AnMe3z/VMKS/hardware/exports/exoskeleton parts-Short part.stl

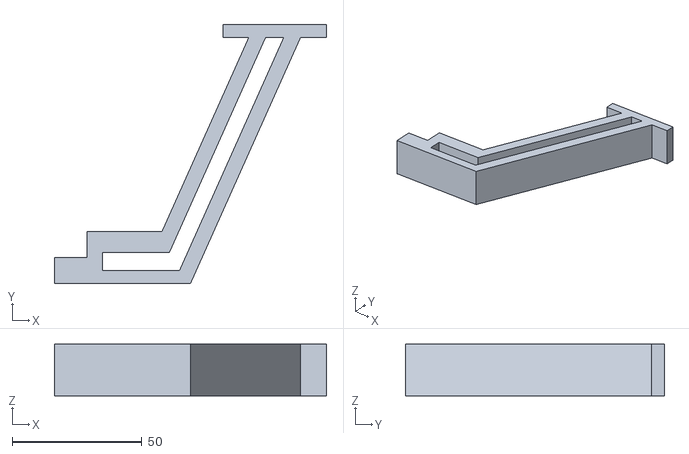
[picture p24: CAD file, 2023-04-21]
hardware/exports/exoskeleton parts-Short part.stl
105.0 x 100.0 x 20.0
