AnMe3z/VMKS/hardware/holders/ultrasonicHolder-Body.stl

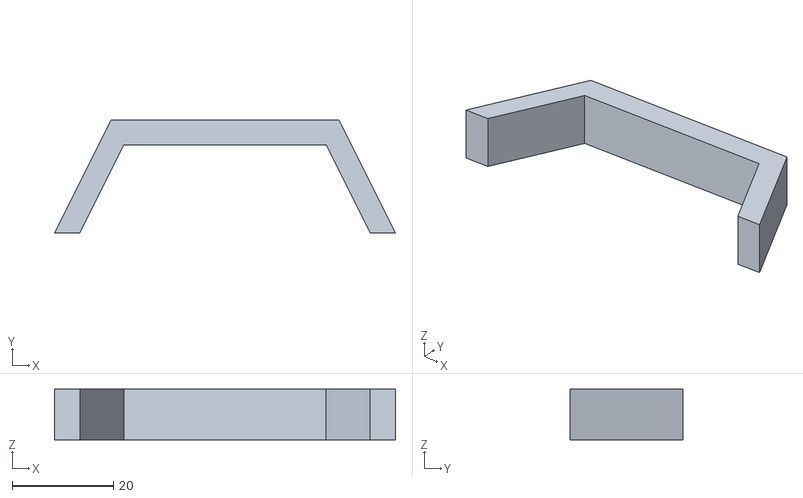
[picture p25: CAD file, 2023-04-12]
hardware/holders/ultrasonicHolder-Body.stl
67.4 x 22.4 x 10.0
