AnMe3z/VMKS/hardware/legs/knee.FCStd

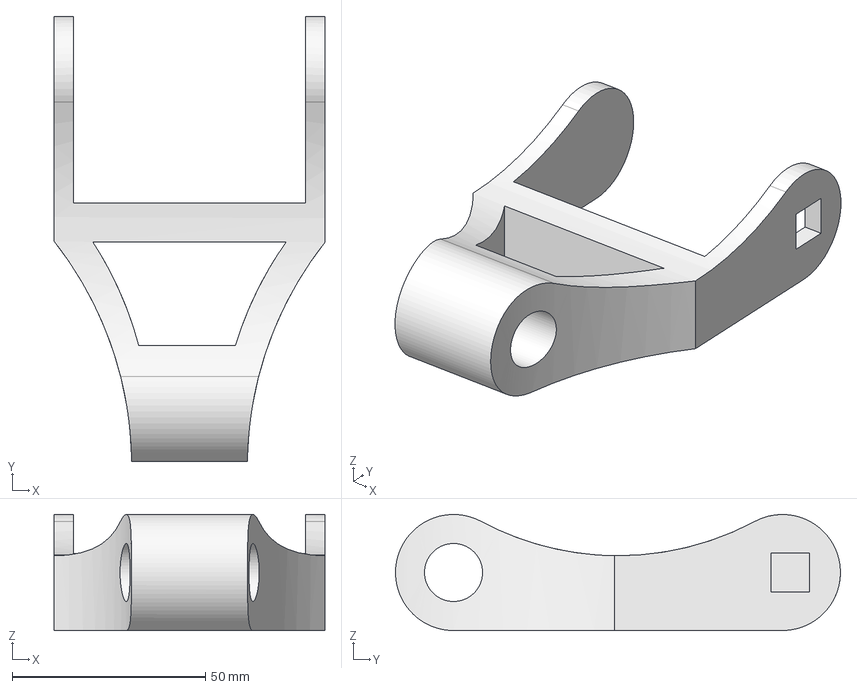
[picture p26: CAD file, 2022-12-15]
hardware/legs/knee.FCStd
70.0 x 115.0 x 30.0 mm
