AnMe3z/VMKS/hardware/legs/testModels/upperLeg.FCStd

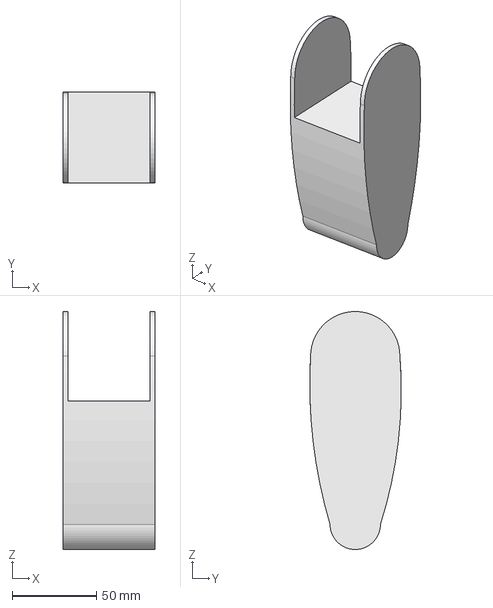
[picture p27: CAD file, 2022-11-03]
hardware/legs/testModels/upperLeg.FCStd
55.0 x 54.4 x 141.6 mm
