AnMe3z/VMKS/hardware/exports/Unnamed-hip-femaleWith_Connectors2-right.stl

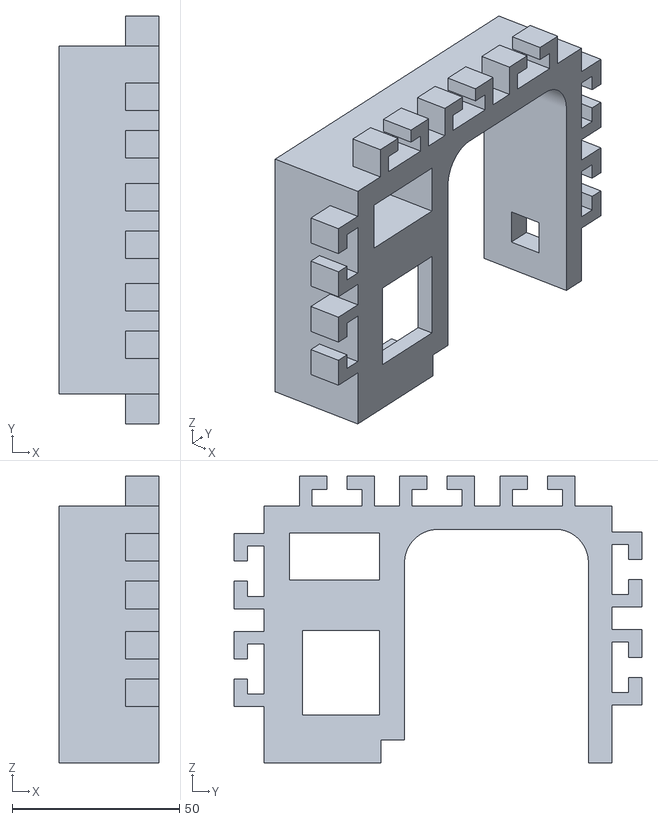
[picture p28: CAD file, 2023-01-17]
hardware/exports/Unnamed-hip-femaleWith_Connectors2-right.stl
30.0 x 122.0 x 85.9
