AnMe3z/VMKS/hardware/legs/testModels/combinedLegRotated_v2.FCStd

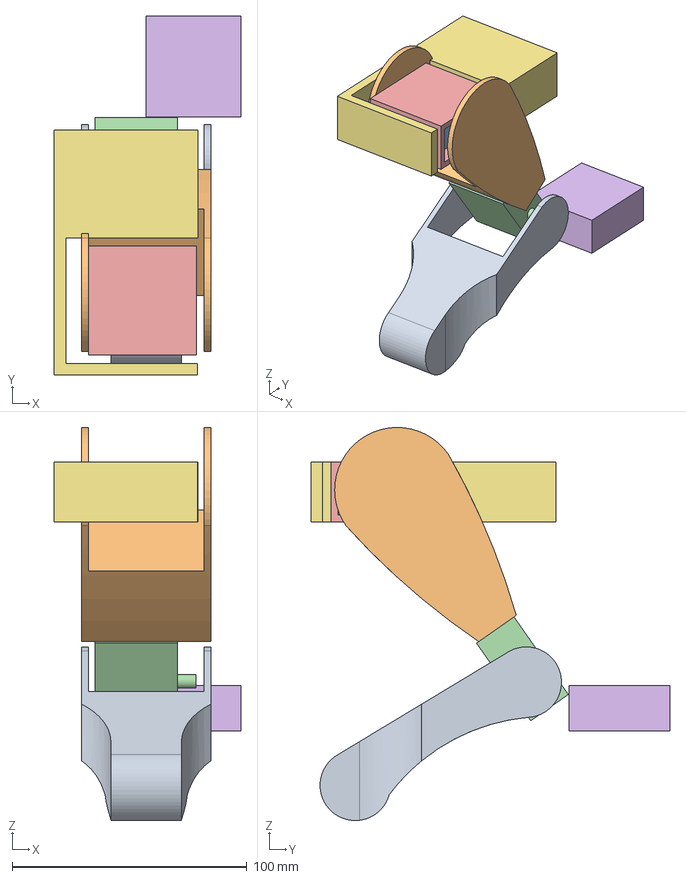
[picture p29: CAD file, 2022-11-03]
hardware/legs/testModels/combinedLegRotated_v2.FCStd
79.5 x 152.8 x 167.3 mm
lowerLegBody
upperLegBody
femurServoBody
kneeServoBody
FemurBody
HipServoBody
HipBody
