AnMe3z/VMKS/hardware/body/OtherBodyParts-andrey.FCStd

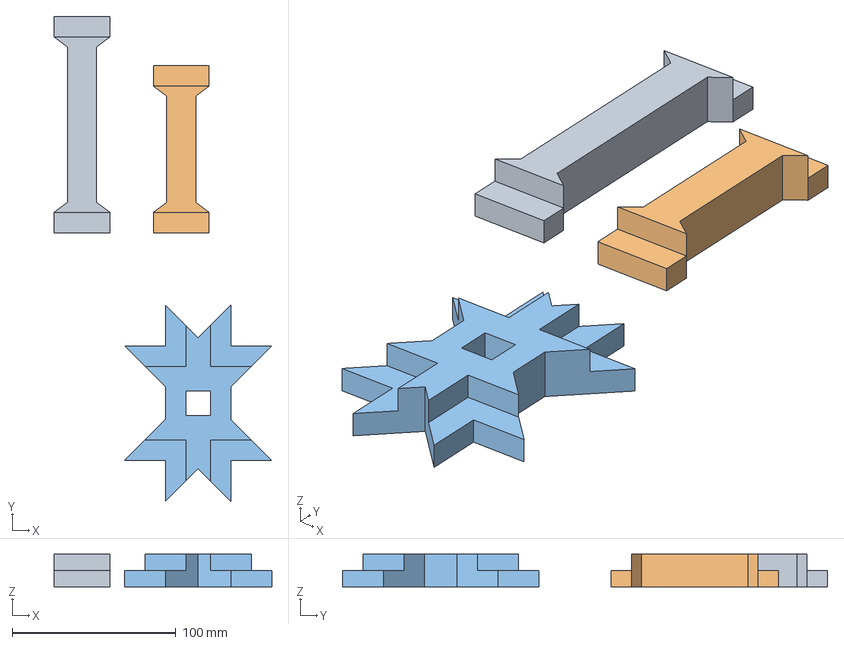
[picture p30: CAD file, 2023-01-09]
hardware/body/OtherBodyParts-andrey.FCStd
132.9 x 296.0 x 20.0 mm
I
I2 (4cm)
Star
