AnMe3z/VMKS/hardware/legs/hip-joint-pin.FCStd

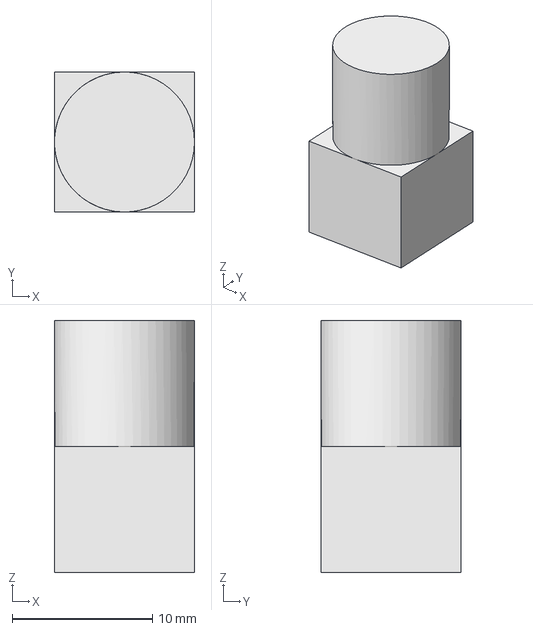
[picture p31: CAD file, 2022-12-09]
hardware/legs/hip-joint-pin.FCStd
10.0 x 10.0 x 18.0 mm
