AnMe3z/VMKS/hardware/legs/testModels/lowerLeg.FCStd

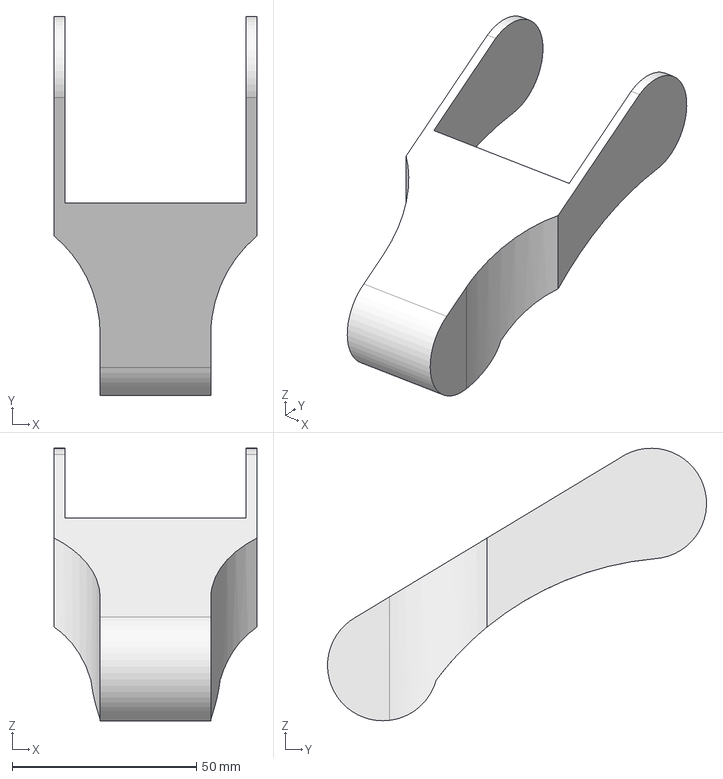
[picture p32: CAD file, 2022-11-03]
hardware/legs/testModels/lowerLeg.FCStd
55.0 x 102.8 x 73.9 mm
