AnMe3z/VMKS/hardware/exports/l1.stl

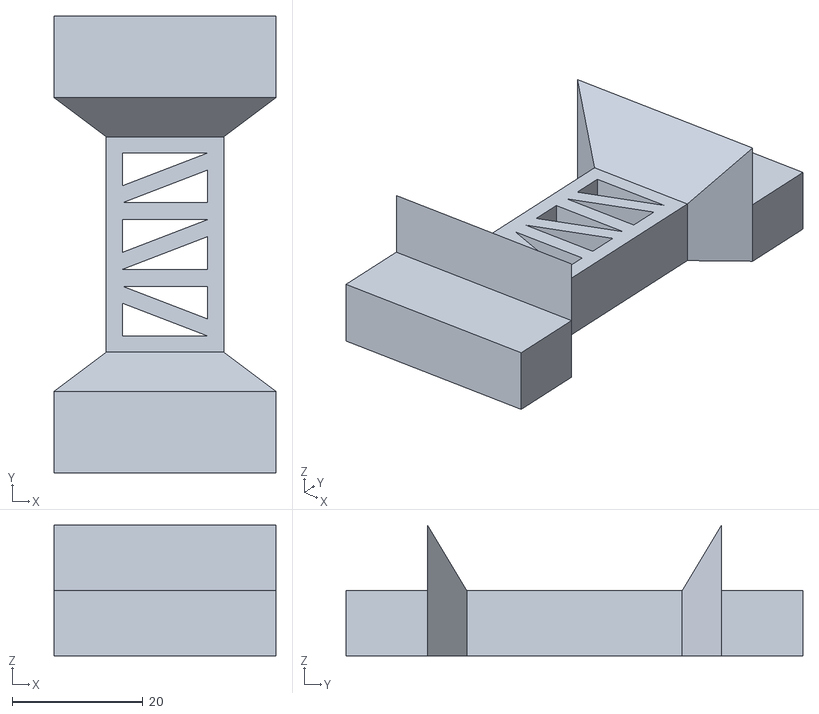
[picture p33: CAD file, 2023-01-11]
hardware/exports/l1.stl
34.0 x 70.0 x 20.0
