AnMe3z/VMKS/hardware/legs/hip-male.FCStd

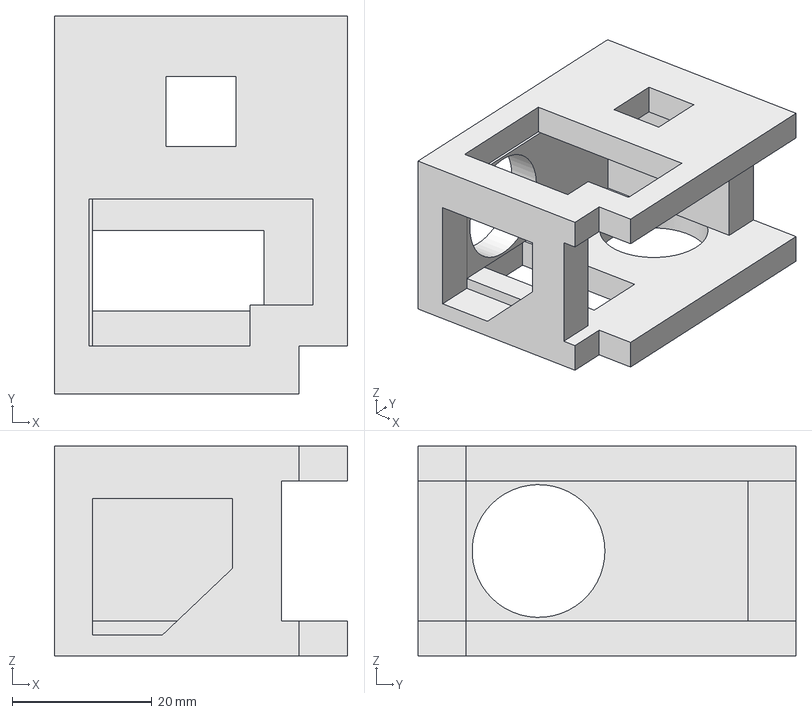
[picture p34: CAD file, 2022-12-09]
hardware/legs/hip-male.FCStd
42.0 x 54.1 x 30.0 mm
