AnMe3z/VMKS/hardware/body/hip-femaleWith_Connectors_Fixed_Positioning (1).FCStd

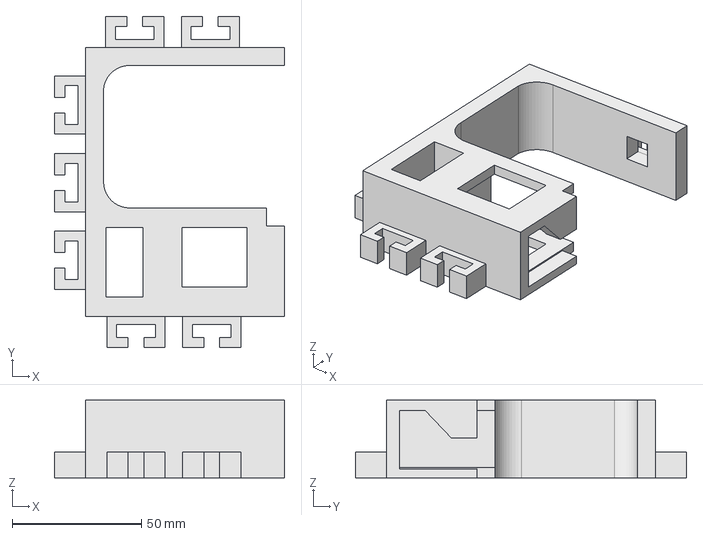
[picture p35: CAD file, 2022-12-19]
hardware/body/hip-femaleWith_Connectors_Fixed_Positioning (1).FCStd
88.9 x 128.0 x 30.0 mm
