AnMe3z/VMKS/hardware/legs/joint_pin.FCStd

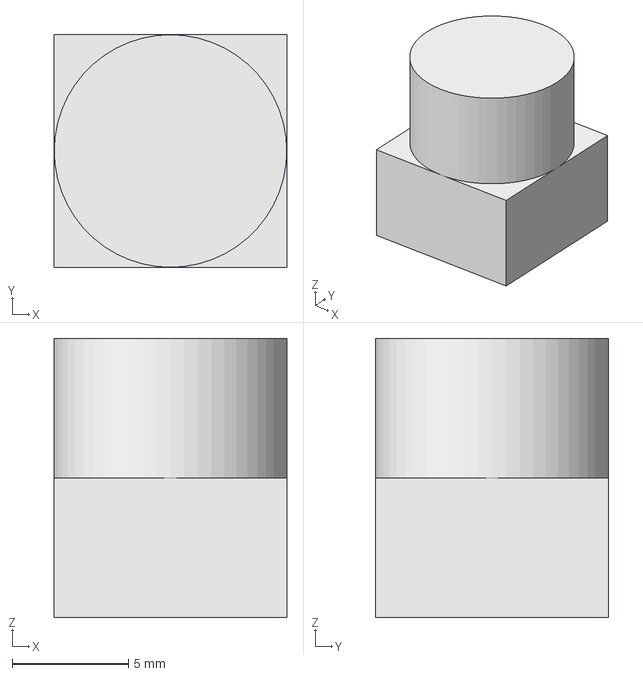
[picture p36: CAD file, 2022-12-09]
hardware/legs/joint_pin.FCStd
10.0 x 10.0 x 12.0 mm
