AnMe3z/VMKS/hardware/legs/testModels/hip_01.FCStd

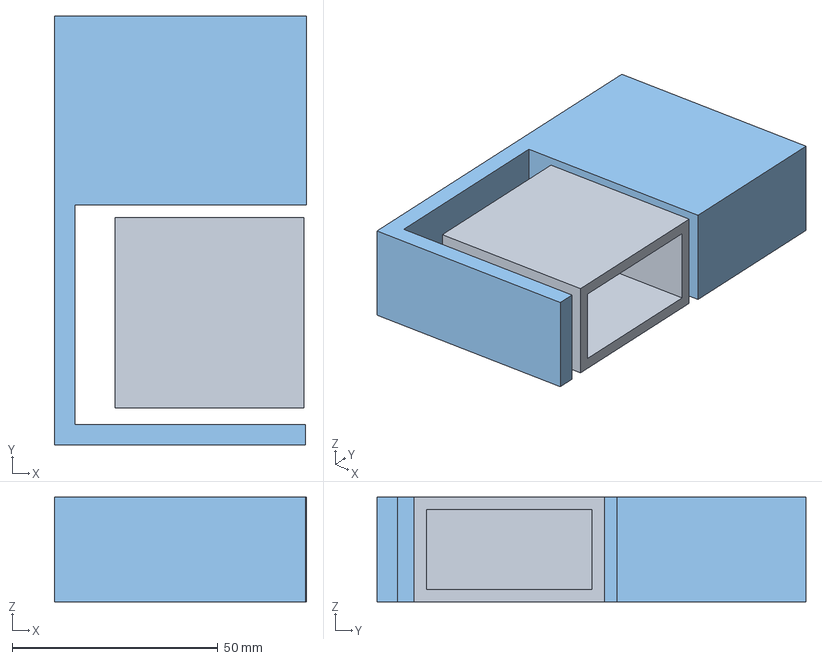
[picture p37: CAD file, 2022-11-03]
hardware/legs/testModels/hip_01.FCStd
61.3 x 104.3 x 25.5 mm
FemurBody
HipServoBody
