AnMe3z/VMKS/hardware/body/hip-female(With Connectors).FCStd

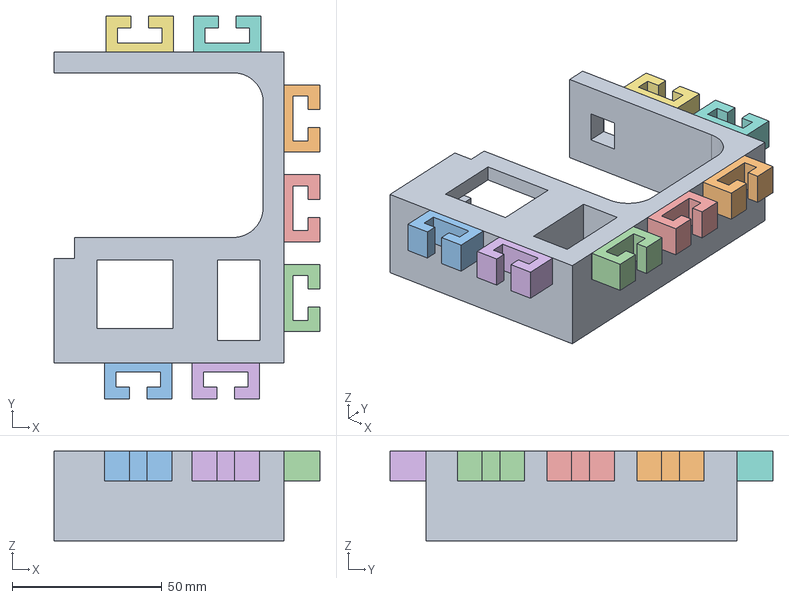
[picture p38: CAD file, 2022-12-18]
hardware/body/hip-female(With Connectors).FCStd
88.9 x 128.0 x 30.0 mm
Female7
Female1
Female5
Female6
Female2
Female3
Female4
