AnMe3z/VMKS/hardware/exports/HipToBody.stl

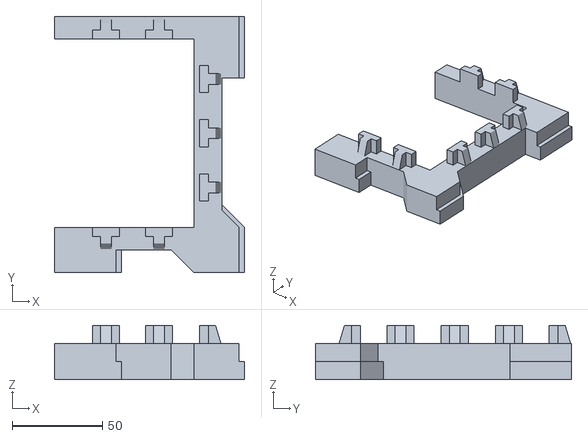
[picture p39: CAD file, 2023-01-09]
hardware/exports/HipToBody.stl
105.0 x 141.5 x 30.0
