AnMe3z/VMKS/hardware/legs/hip-serv-joint-pin.FCStd

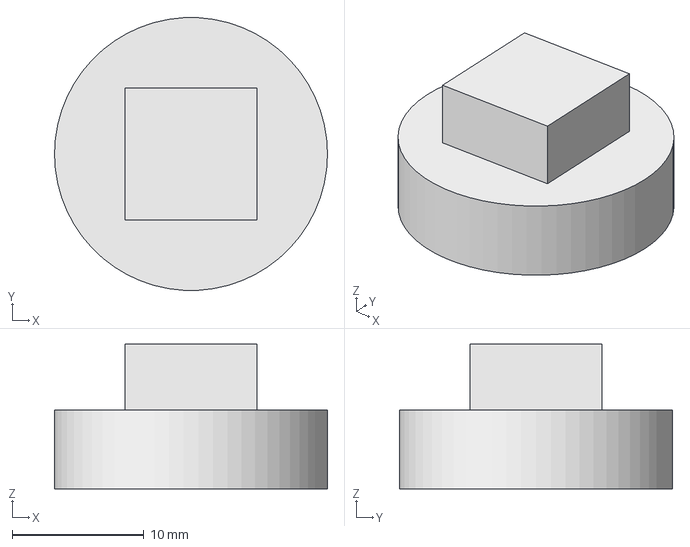
[picture p40: CAD file, 2022-12-09]
hardware/legs/hip-serv-joint-pin.FCStd
20.8 x 20.7 x 11.0 mm
