AnMe3z/VMKS/hardware/legs/knee_concept.FCStd

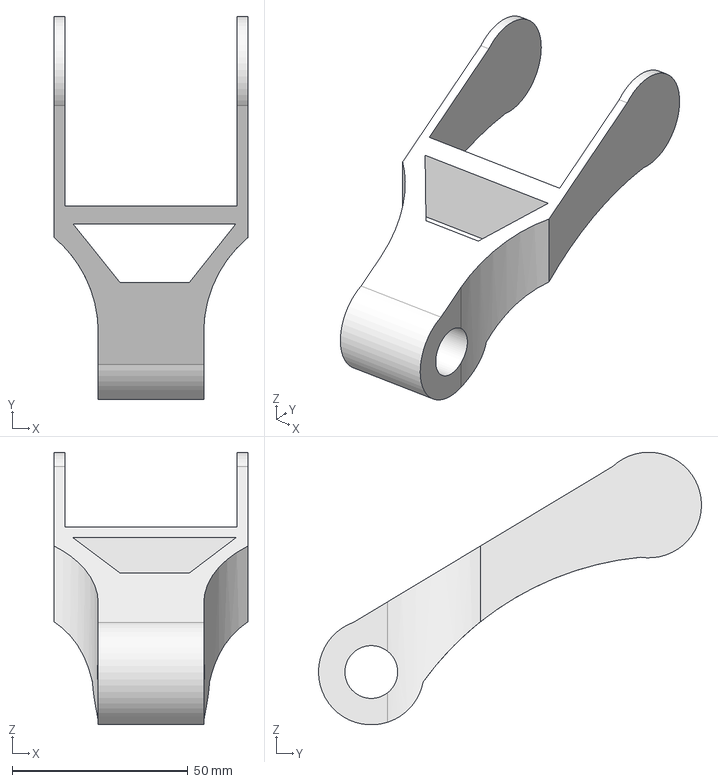
[picture p41: CAD file, 2022-11-12]
hardware/legs/knee_concept.FCStd
55.0 x 108.8 x 77.4 mm
