AnMe3z/VMKS/hardware/legs/testModels/combinedLegRotated.FCStd

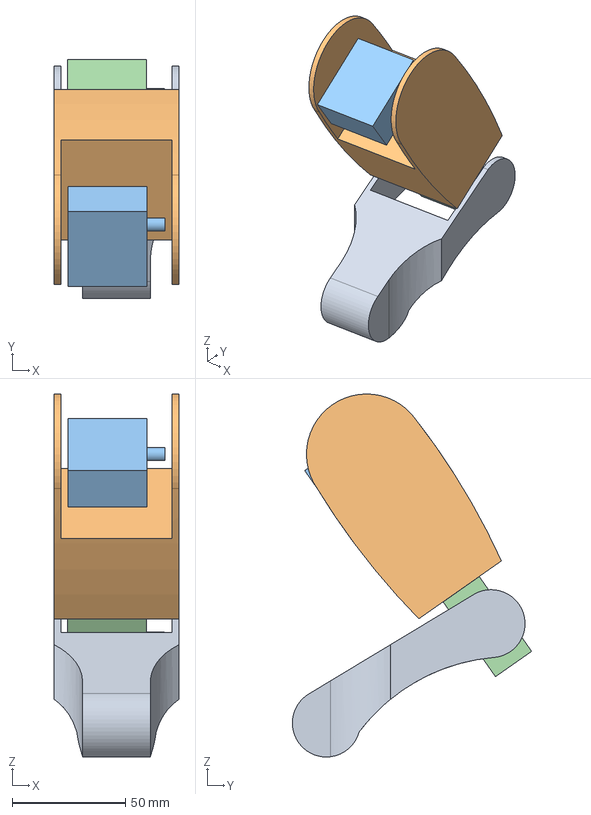
[picture p42: CAD file, 2022-11-03]
hardware/legs/testModels/combinedLegRotated.FCStd
55.0 x 105.7 x 160.3 mm
lowerLegBody
upperLegBody
femurServoBody
kneeServoBody
