AnMe3z/VMKS/hardware/legs/femur_messy.FCStd

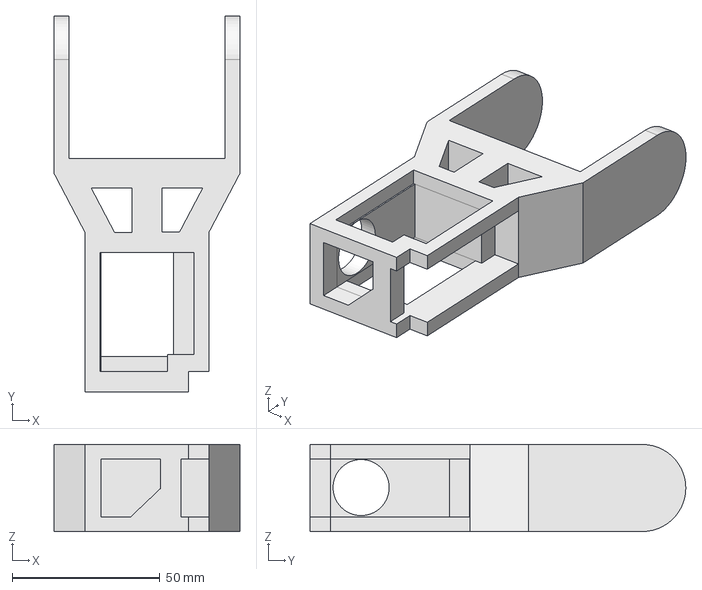
[picture p43: CAD file, 2022-11-10]
hardware/legs/femur_messy.FCStd
63.0 x 127.3 x 29.5 mm
