AnMe3z/VMKS/hardware/legs/testModels/servoRealistic.FCStd

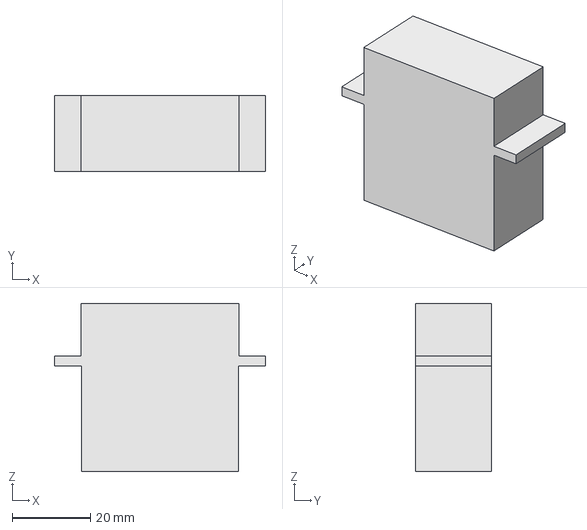
[picture p44: CAD file, 2022-11-03]
hardware/legs/testModels/servoRealistic.FCStd
53.9 x 19.5 x 43.0 mm
