AnMe3z/VMKS/hardware/exports/leg-render-1.stl

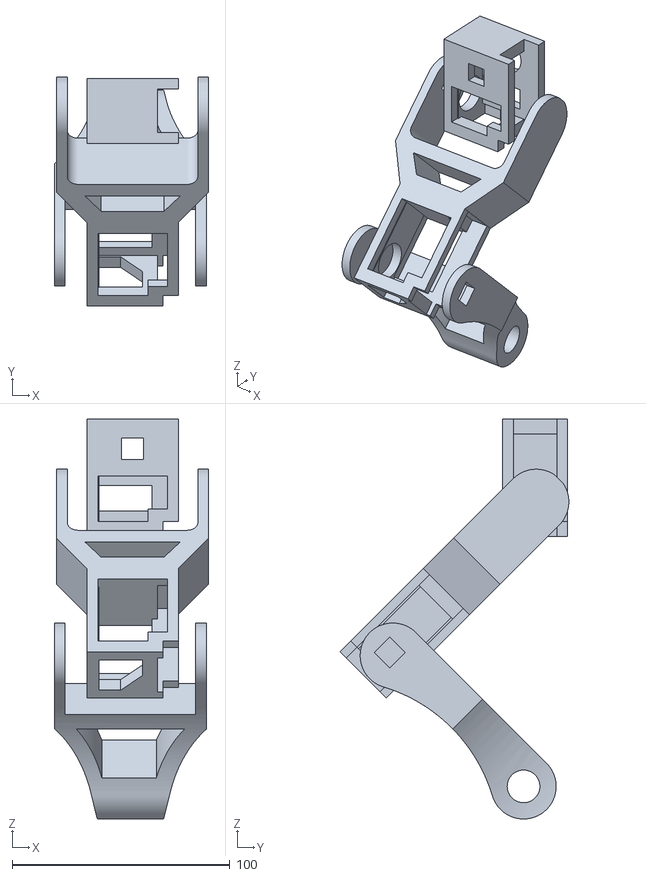
[picture p45: CAD file, 2023-01-09]
hardware/exports/leg-render-1.stl
71.0 x 105.2 x 183.9
