AnMe3z/VMKS/hardware/legs/testModels/hip.FCStd

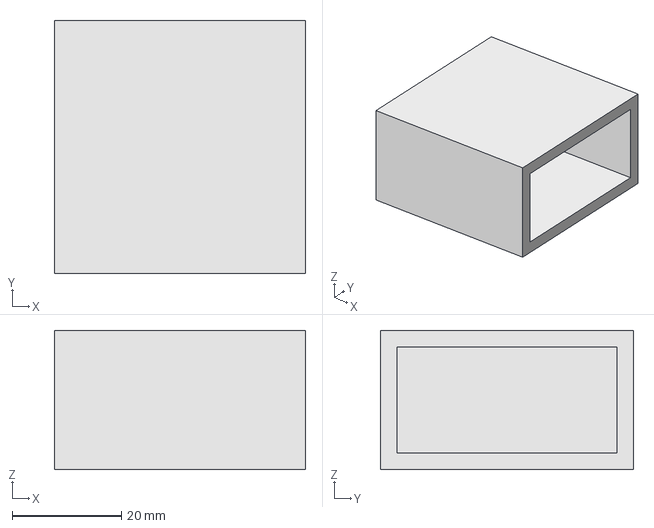
[picture p46: CAD file, 2022-11-03]
hardware/legs/testModels/hip.FCStd
46.0 x 46.3 x 25.5 mm
