AnMe3z/VMKS/hardware/exports/l2.stl

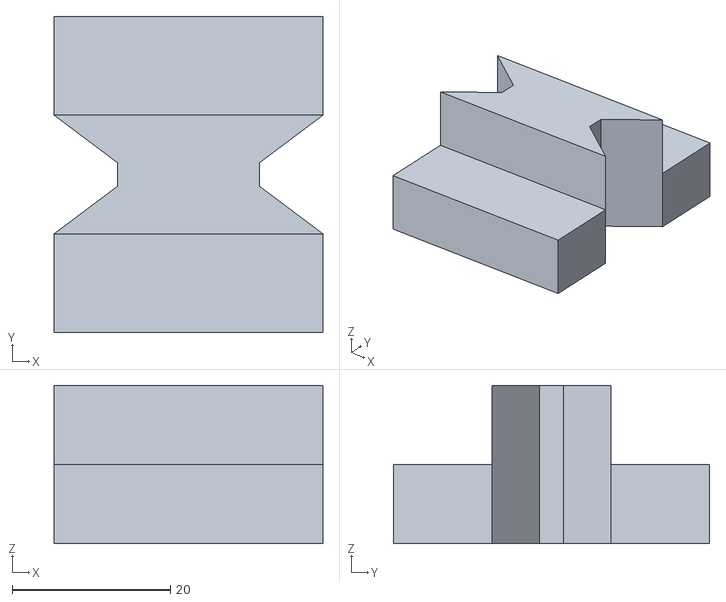
[picture p47: CAD file, 2023-01-09]
hardware/exports/l2.stl
34.0 x 40.0 x 20.0
