AnMe3z/VMKS/hardware/legs/testModels/servo.FCStd

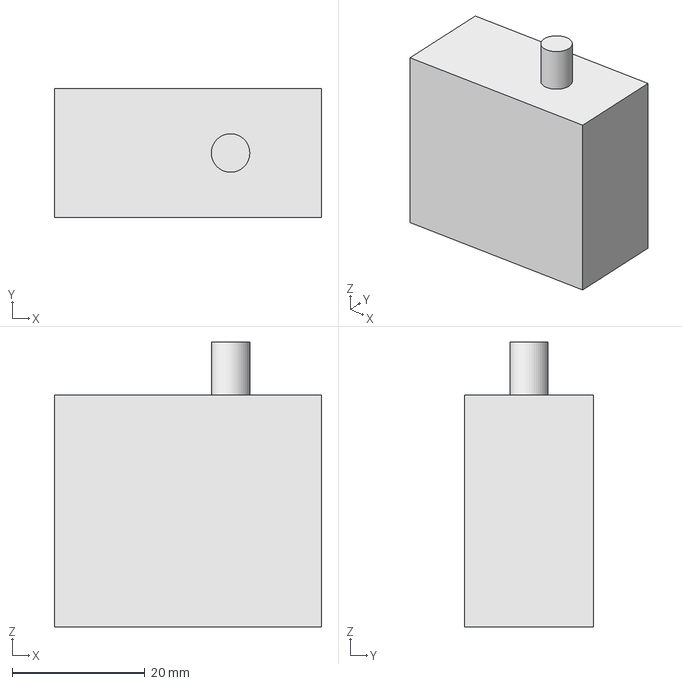
[picture p48: CAD file, 2022-11-03]
hardware/legs/testModels/servo.FCStd
40.3 x 19.5 x 43.0 mm
