AnMe3z/VMKS/hardware/exports/Star.stl

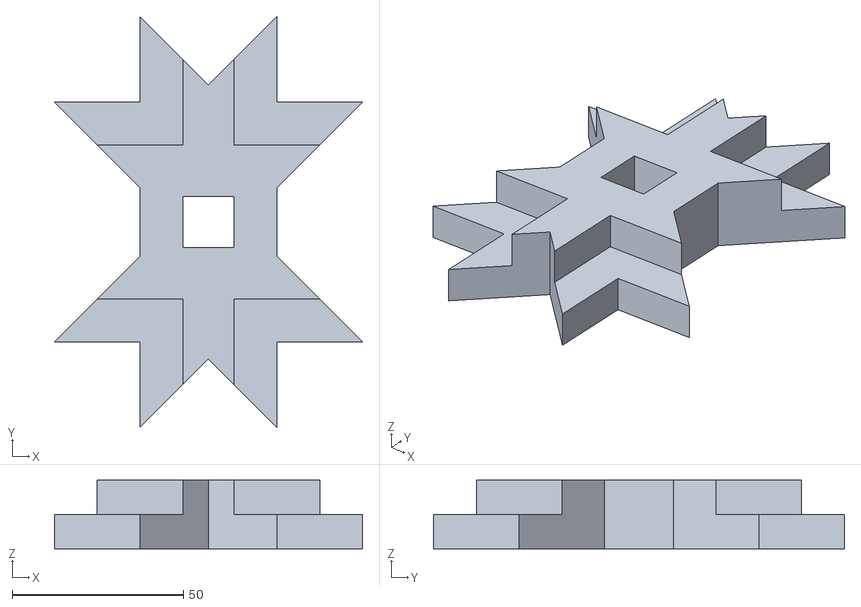
[picture p49: CAD file, 2023-01-09]
hardware/exports/Star.stl
90.0 x 120.0 x 20.0
