AnMe3z/VMKS/hardware/exports/leg-render-2.stl

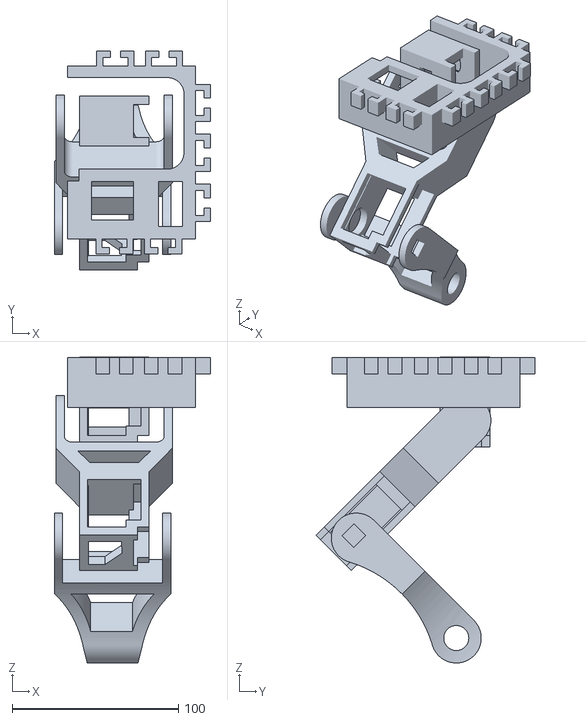
[picture p50: CAD file, 2023-01-09]
hardware/exports/leg-render-2.stl
94.0 x 131.6 x 183.9
