AnMe3z/VMKS/hardware/exports/OtherBodyParts-I2-4cm.stl

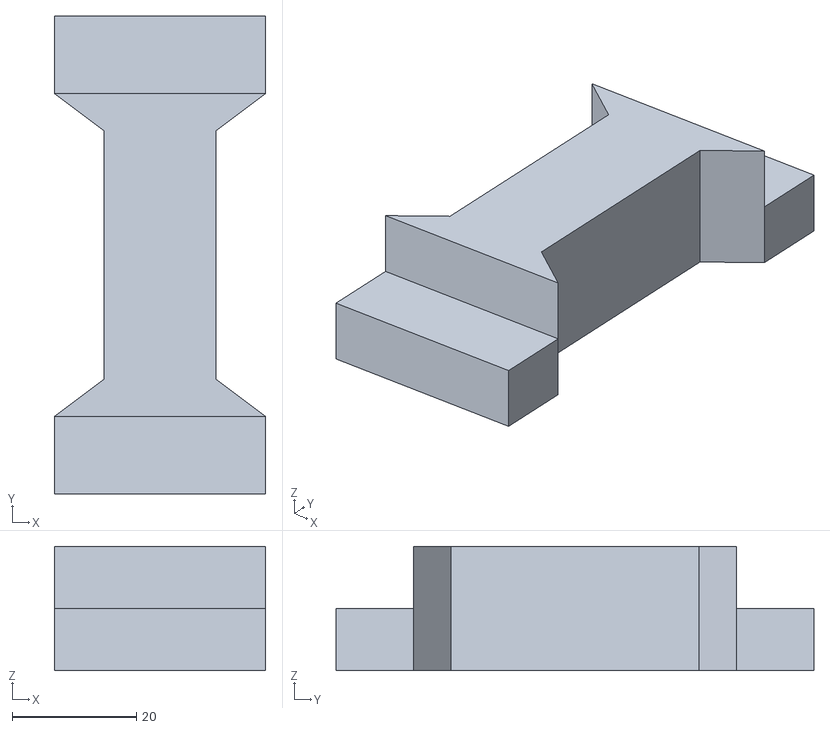
[picture p51: CAD file, 2022-12-19]
hardware/exports/OtherBodyParts-I2-4cm.stl
34.0 x 77.0 x 20.0
