AnMe3z/VMKS/hardware/exports/knee-Body.stl

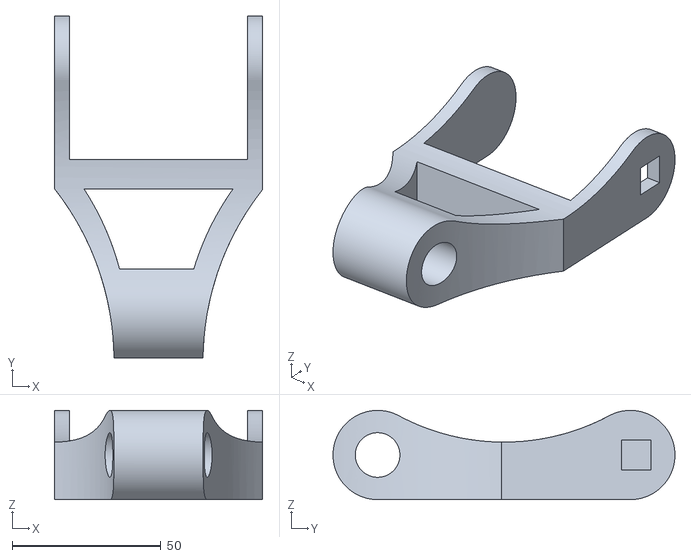
[picture p52: CAD file, 2022-12-15]
hardware/exports/knee-Body.stl
70.0 x 115.0 x 30.0
