AnMe3z/VMKS/code/wifi-influxdb/wifi-influxdb.ino

#if defined(ESP32)
  #include <WiFiMulti.h>
  WiFiMulti wifiMulti;
  #define DEVICE "ESP32"
  #elif defined(ESP8266)
  #include <ESP8266WiFiMulti.h>
  ESP8266WiFiMulti wifiMulti;
  #define DEVICE "ESP8266"
  #endif
  
  #include <InfluxDbClient.h>
  #include <InfluxDbCloud.h>
  
  // WiFi AP SSID
  #define WIFI_SSID "Pitko"
  // WiFi password
  #define WIFI_PASSWORD "n0name0024"
  
  #define INFLUXDB_URL "http://192.168.1.100:8086"
  #define INFLUXDB_TOKEN "KS4kaMCQITm1_1IWgAggj1aFntXpbc0NE2us2T-trBmuu6hDl-rGuQtFRgZ-CAwy6Gt1_V-vK8yzVD8c0AONGQ=="
  #define INFLUXDB_ORG "0f255d040cf7490d"
  #define INFLUXDB_BUCKET "gosho-flexa-samokov"
  
  // Time zone info
  #define TZ_INFO "UTC3"
  
  // Declare InfluxDB client instance with preconfigured InfluxCloud certificate
  InfluxDBClient client(INFLUXDB_URL, INFLUXDB_ORG, INFLUXDB_BUCKET, INFLUXDB_TOKEN, InfluxDbCloud2CACert);
  
  // Declare Data point
  Point sensor("wifi_status");
  
  void setup() {
    Serial.begin(115200);
  
    // Setup wifi
    WiFi.mode(WIFI_STA);
    wifiMulti.addAP(WIFI_SSID, WIFI_PASSWORD);
  
    Serial.print("Connecting to wifi");
    while (wifiMulti.run() != WL_CONNECTED) {
      Serial.print(".");
      delay(100);
    }
    Serial.println();
  
    // Accurate time is necessary for certificate validation and writing in batches
    // We use the NTP servers in your area as provided by: https://www.pool.ntp.org/zone/
    // Syncing progress and the time will be printed to Serial.
    timeSync(TZ_INFO, "pool.ntp.org", "time.nis.gov");
  
  
    // Check server connection
    if (client.validateConnection()) {
      Serial.print("Connected to InfluxDB: ");
      Serial.println(client.getServerUrl());
    } else {
      Serial.print("InfluxDB connection failed: ");
      Serial.println(client.getLastErrorMessage());
    }
  }
  void loop() {}
