AnMe3z/VMKS/code/other/stage1/servos/servo-test-1/servo-test-1.ino

//Libraries
#include <Wire.h>//https://www.arduino.cc/en/reference/wire
#include <Adafruit_PWMServoDriver.h>//https://github.com/adafruit/Adafruit-PWM-Servo-Driver-Library
//Constants
#define nbPCAServo 16
//Parameters
int MIN_IMP [nbPCAServo] ={500, 500, 500, 500, 500, 500, 500, 500, 500, 500, 500, 500, 500, 500, 500, 500};
int MAX_IMP [nbPCAServo] ={2500, 2500, 2500, 2500, 2500, 2500, 2500, 2500, 2500, 2500, 2500, 2500, 2500, 2500, 2500, 2500};
int MIN_ANG [nbPCAServo] ={80, 80, 80, 80, 80, 80, 80, 80, 80, 80, 80, 80, 80, 80, 80, 80};
int MAX_ANG [nbPCAServo] ={90, 90, 90, 90, 90, 90, 90, 90, 90, 90, 90, 90, 90, 90, 90, 90};
//Objects
Adafruit_PWMServoDriver pca= Adafruit_PWMServoDriver(0x40);
void setup(){
//Init Serial USB
Serial.begin(9600);
Serial.println(F("Initialize System"));
pca.begin();
pca.setPWMFreq(60);  // Analog servos run at ~60 Hz updates
}
void loop(){
  pcaScenario();
}
void pcaScenario(){/* function pcaScenario */
////Scenario to test servomotors controlled by PCA9685 I2C Module
for (int i=0; i<nbPCAServo; i++) {
  Serial.print("Servo");
  Serial.println(i);
      //int middleVal=((MAX_IMP[i]+MIN_IMP[i])/2)/20000*4096; // conversion µs to pwmval
      //pca.setPWM(i,0,middleVal);
      for(int pos=(MAX_IMP[i]+MIN_IMP[i])/2;pos<MAX_IMP[i];pos+=10){
        pca.writeMicroseconds(i,pos);delay(10);
      }
      for(int pos=MAX_IMP[i];pos>MIN_IMP[i];pos-=10){
        pca.writeMicroseconds(i,pos);delay(10);
      }
      for(int pos=MIN_IMP[i];pos<(MAX_IMP[i]+MIN_IMP[i])/2;pos+=10){
        pca.writeMicroseconds(i,pos);delay(10);
      }
      pca.setPin(i,0,true); // deactivate pin i
    }
}
int jointToImp(double x,int i){/* function jointToImp */
////Convert joint angle into pwm command value
      int imp=(x - MIN_ANG[i]) * (MAX_IMP[i]-MIN_IMP[i]) / (MAX_ANG[i]-MIN_ANG[i]) + MIN_IMP[i];
      imp=max(imp,MIN_IMP[i]);
      imp=min(imp,MAX_IMP[i]);
 return imp;
}
